RBSC/Unimapper/Pics/UniMapper_v2.0.jpg

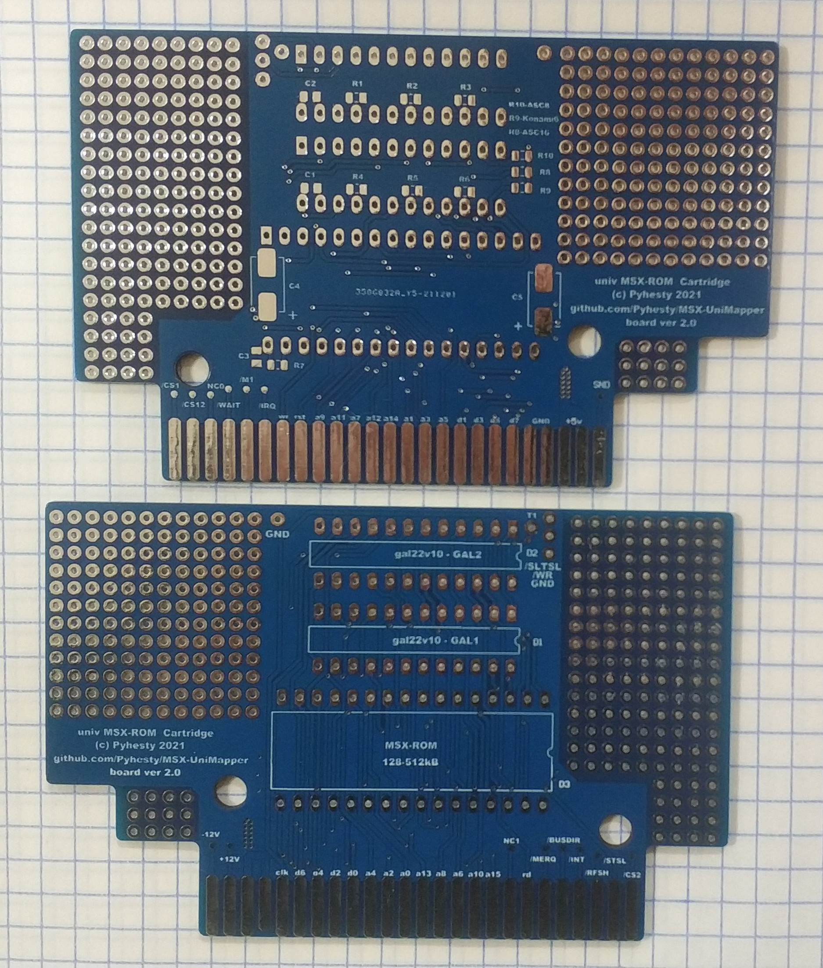
Pics/UniMapper_v2.0.jpg
