RBSC/Unimapper/Pics/UniMapper_v2.0_RBSC.jpg

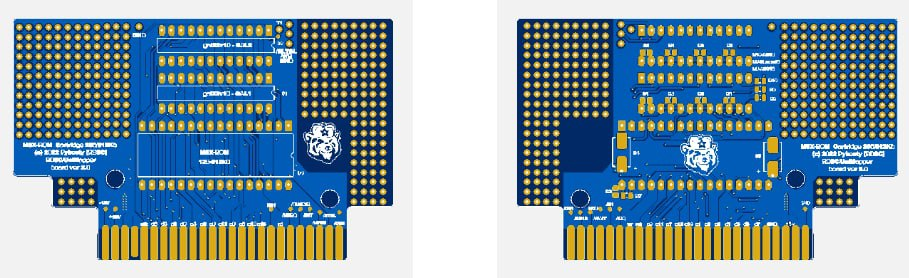
Pics/UniMapper_v2.0_RBSC.jpg
