RBSC/Unimapper/Pics/UniMapper_v3.0_bot.jpg

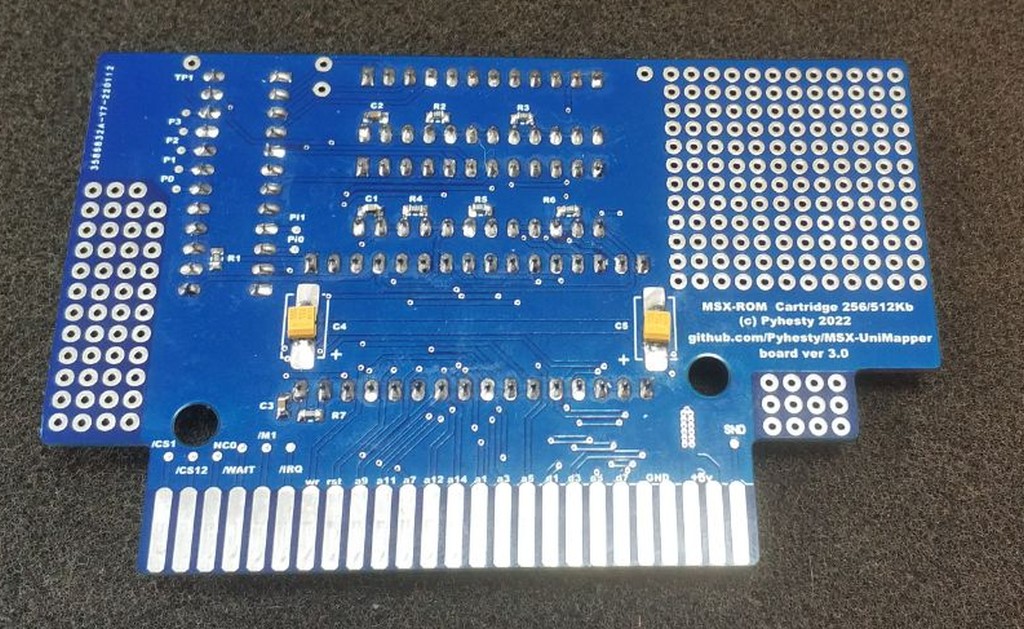
Pics/UniMapper_v3.0_bot.jpg
