RBSC/Unimapper/Pics/UniMapper_v3.0_RBSC.jpg

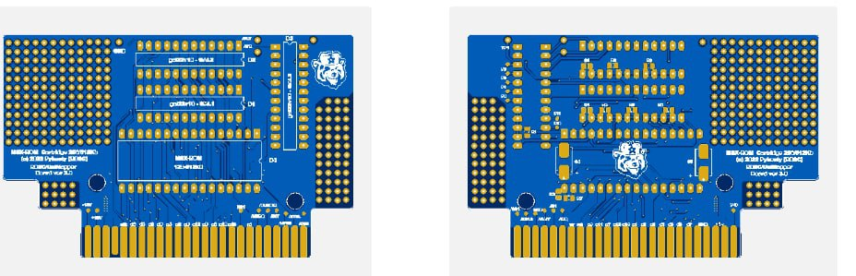
Pics/UniMapper_v3.0_RBSC.jpg
