RBSC/Unimapper/Pics/UniMapper_v3.0_top.jpg

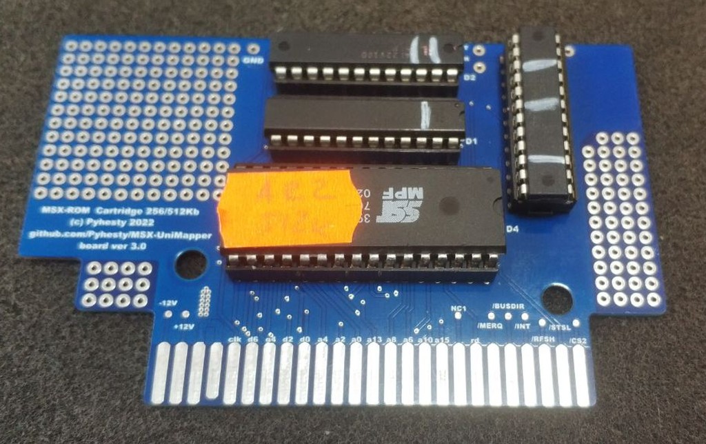
Pics/UniMapper_v3.0_top.jpg
