RBSC/Unimapper/Pics/UniMapper_v3.5_bottom.jpg

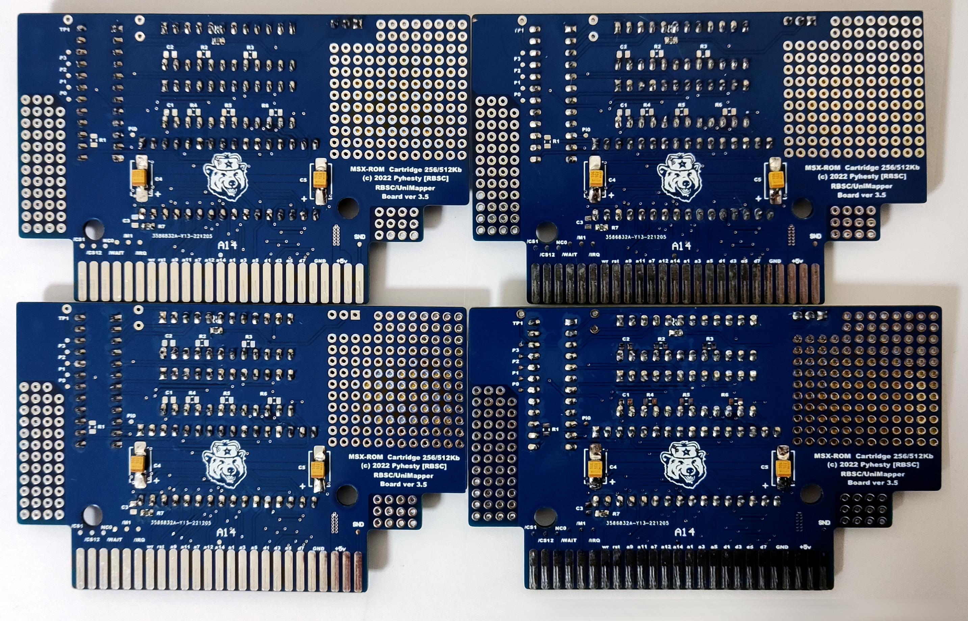
Pics/UniMapper_v3.5_bottom.jpg
