RBSC/Unimapper/Pics/UnimapperBoard.jpg

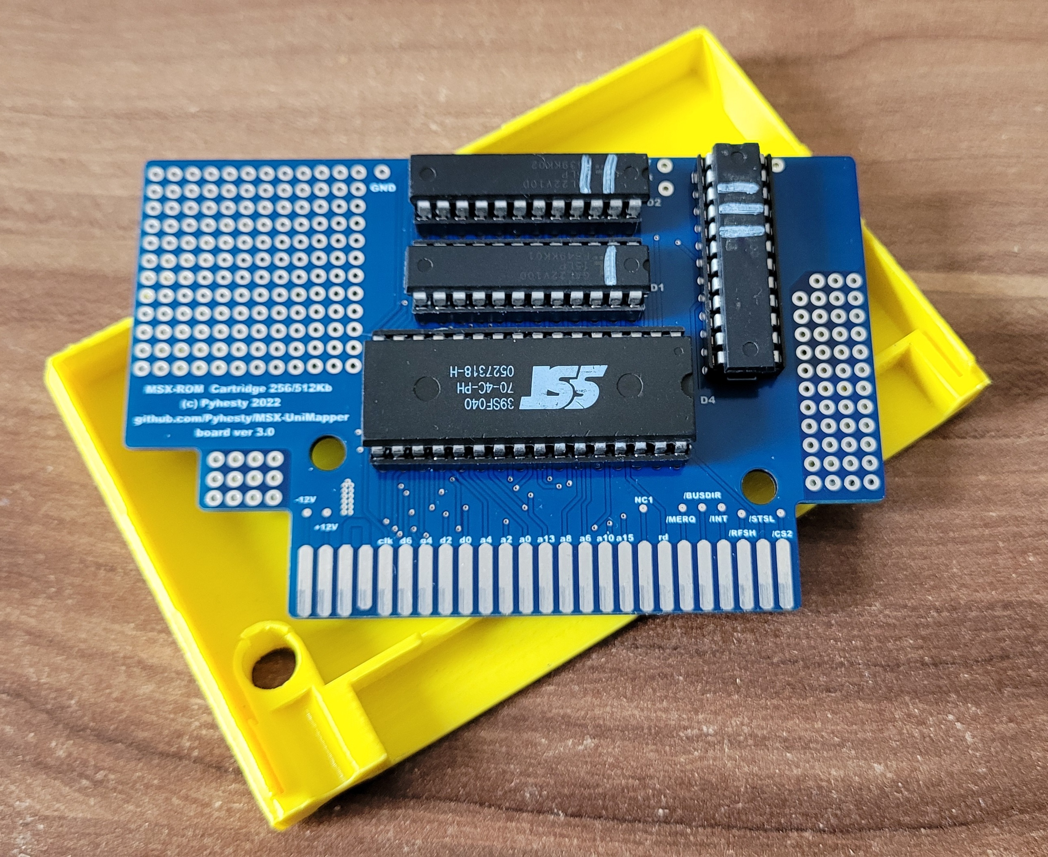
Pics/UnimapperBoard.jpg
