RBSC/Unimapper/Pics/UnimapperBoards_v35.jpg

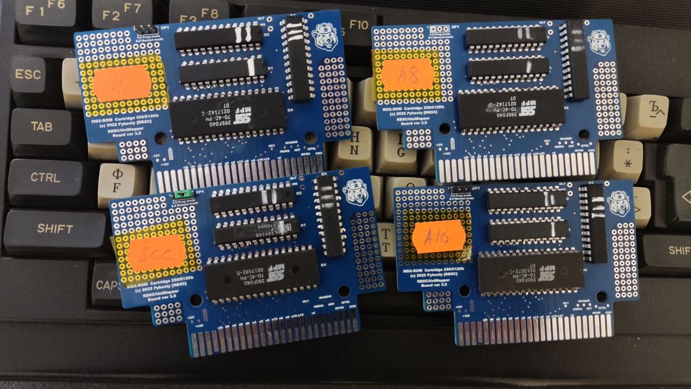
Pics/UnimapperBoards_v35.jpg
