RBSC/Unimapper/Pics/UnimapperCase.jpg

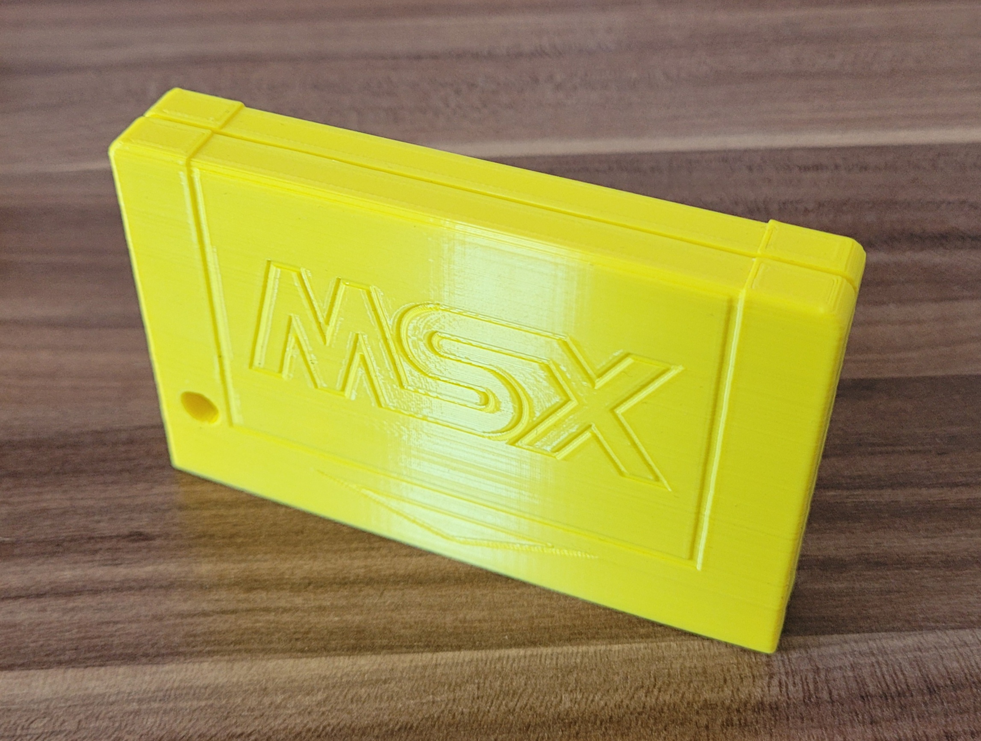
Pics/UnimapperCase.jpg
