RBSC/Unimapper/Test/ASCII8_UMapper_Test/ASCII8_result_256k.jpg

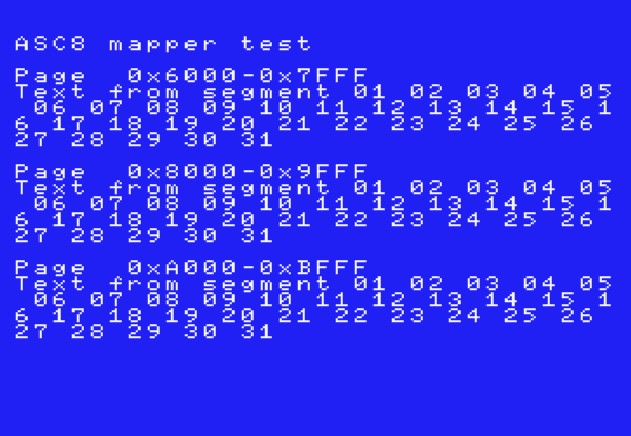
Test/ASCII8_UMapper_Test/ASCII8_result_256k.jpg
