RBSC/Unimapper/Test/ASCII8_UMapper_Test/ASCII8_result_512k.jpg

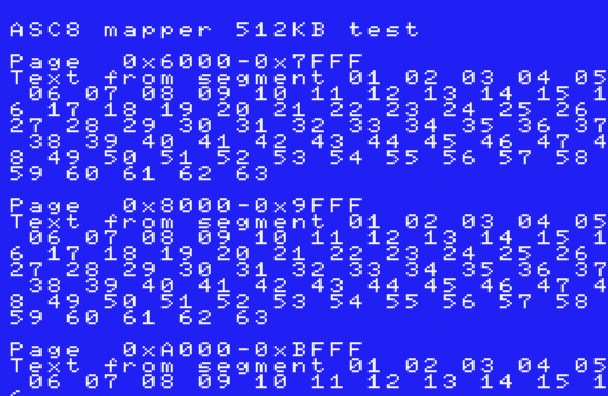
Test/ASCII8_UMapper_Test/ASCII8_result_512k.jpg
