RBSC/Unimapper/Test/ASCII16_UMapper_Test/ASCII16_result_512k.jpg

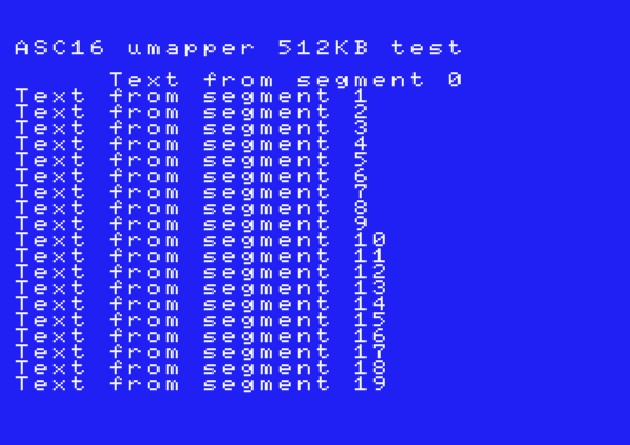
Test/ASCII16_UMapper_Test/ASCII16_result_512k.jpg
