RBSC/Unimapper/Test/Konami4_UMapper_Test/Konami_result_512k.jpg

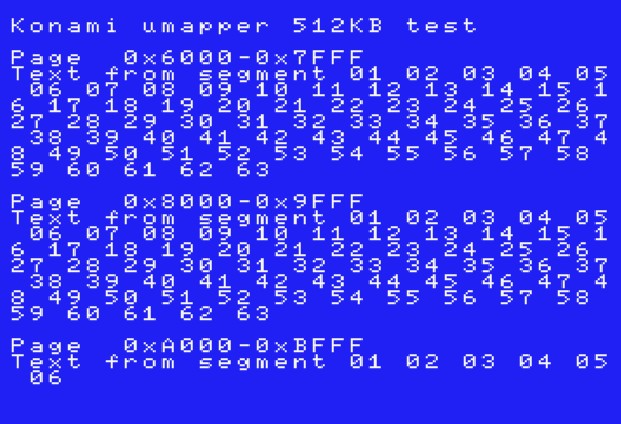
Test/Konami4_UMapper_Test/Konami_result_512k.jpg
