RBSC/Unimapper/Test/KonamiSCC_UMapper_Test/Konami_result_512k.jpg

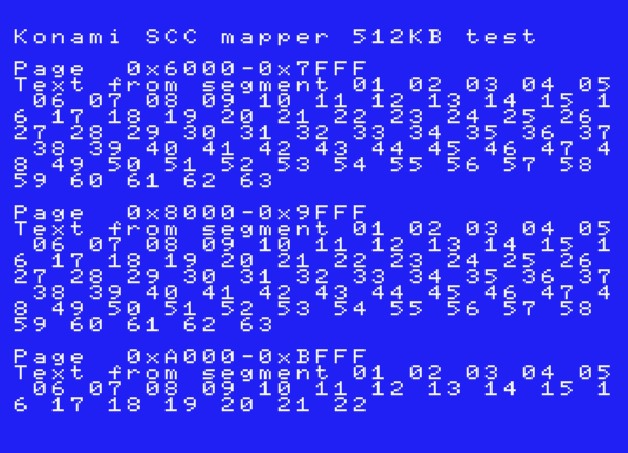
Test/KonamiSCC_UMapper_Test/Konami_result_512k.jpg
